holmos-mikroskop/holmos/3D-druck/Positionsnummern mit Liste.PNG

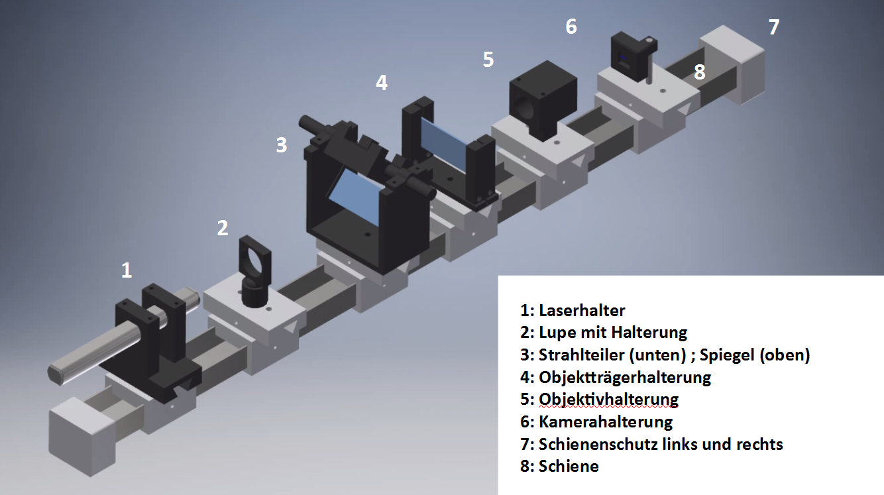
3D-druck/Positionsnummern mit Liste.PNG
