holmos-mikroskop/holmos/doku-img/auswertung-01.png

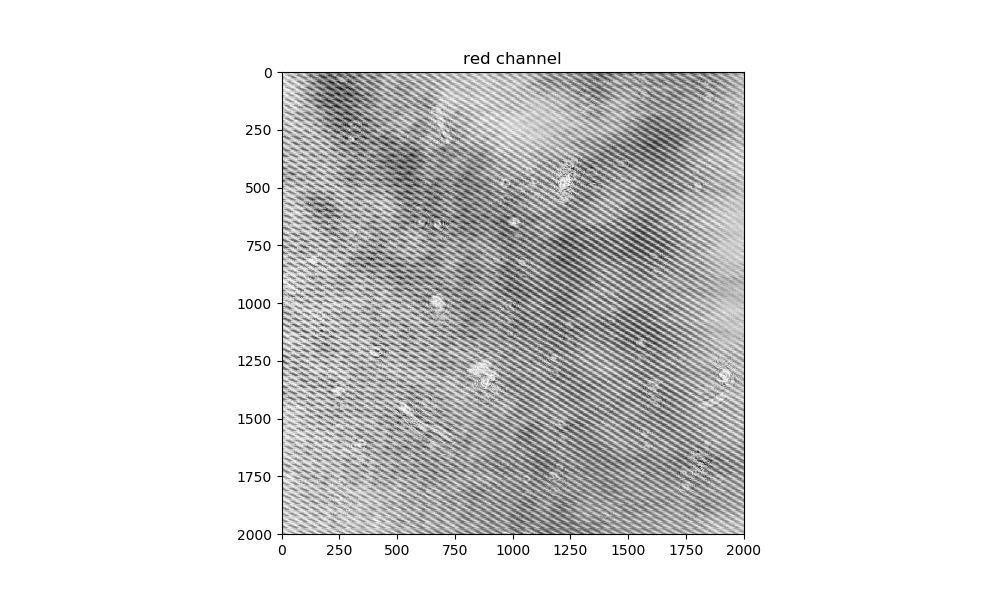
doku-img/auswertung-01.png
