holmos-mikroskop/holmos/doku-img/auswertung-02.png

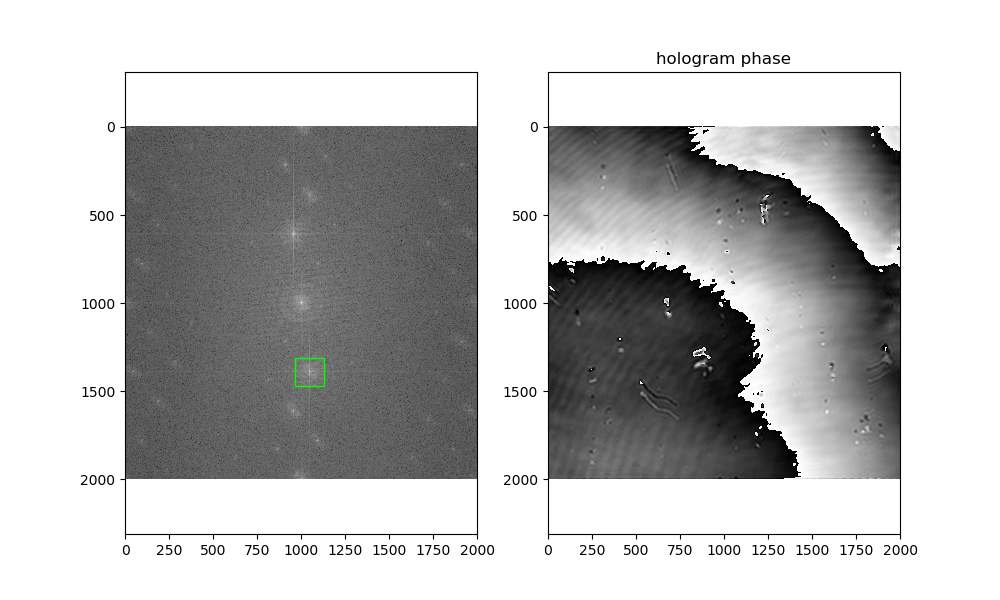
doku-img/auswertung-02.png
