holmos-mikroskop/holmos/doku-img/auswertung-c_001.png

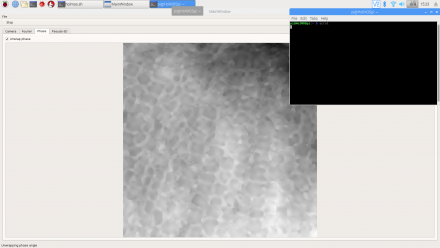
doku-img/auswertung-c_001.png
