holmos-mikroskop/holmos/doku-img/auswertung-c_002.png

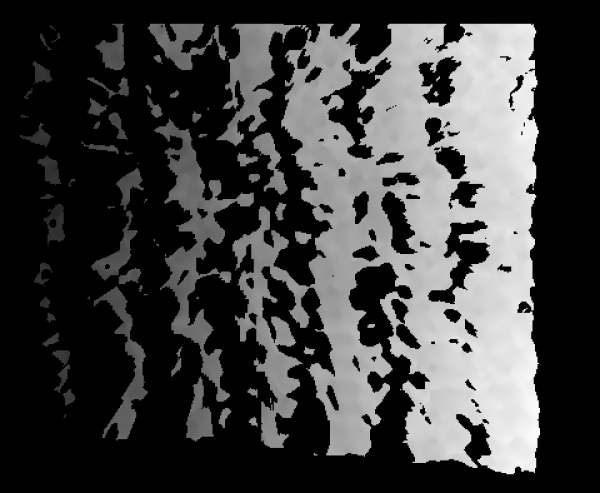
doku-img/auswertung-c_002.png
