holmos-mikroskop/holmos/doku-img/auswertung-c_003.png

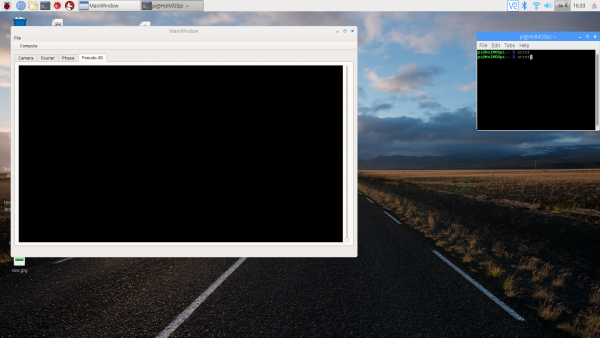
doku-img/auswertung-c_003.png
