holmos-mikroskop/holmos/doku-img/auswertung-c_004.png

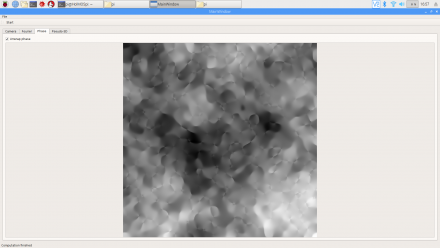
doku-img/auswertung-c_004.png
