holmos-mikroskop/holmos/doku-img/clone_link.jpg

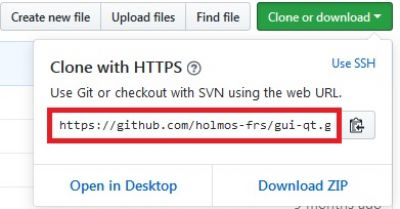
doku-img/clone_link.jpg
