holmos-mikroskop/holmos/doku-img/einfache-auswertung_001.png

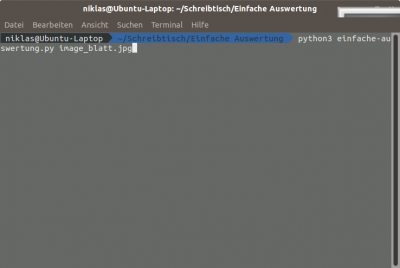
doku-img/einfache-auswertung_001.png
