holmos-mikroskop/holmos/doku-img/einfache-auswertung_002.png

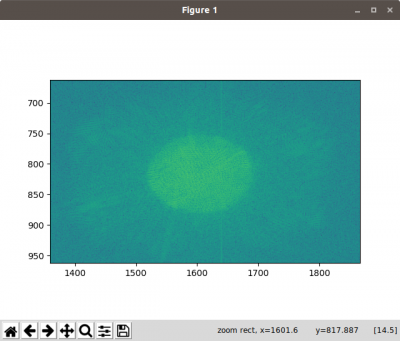
doku-img/einfache-auswertung_002.png
