holmos-mikroskop/holmos/doku-img/einfache-auswertung_003.png

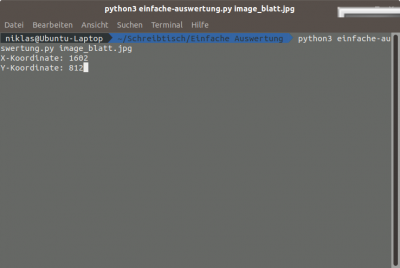
doku-img/einfache-auswertung_003.png
