holmos-mikroskop/holmos/doku-img/einfache-auswertung_005.png

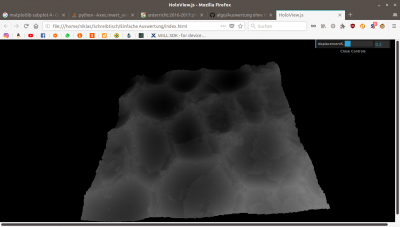
doku-img/einfache-auswertung_005.png
