holmos-mikroskop/holmos/doku-img/erste_interferenz.png

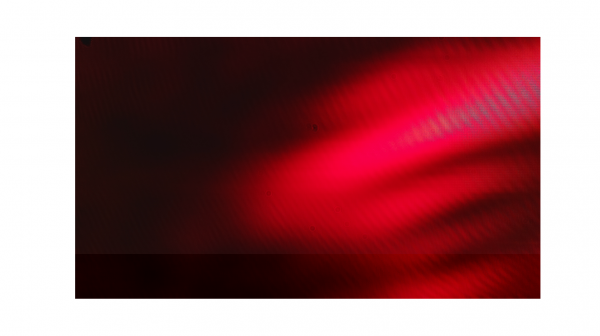
doku-img/erste_interferenz.png
