holmos-mikroskop/holmos/doku-img/first-light.jpg

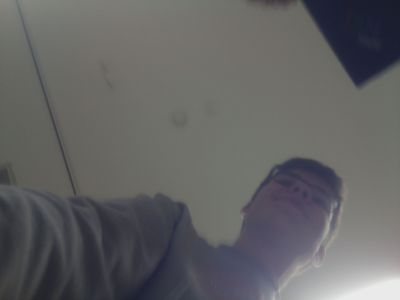
doku-img/first-light.jpg
