holmos-mikroskop/holmos/doku-img/holoview_bsp2_figure1.jpg

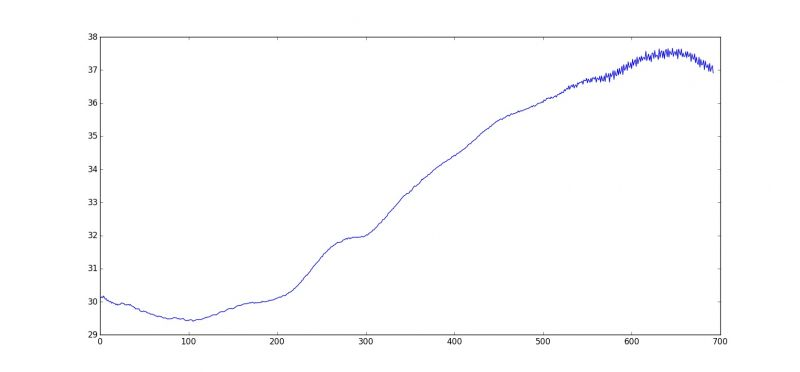
doku-img/holoview_bsp2_figure1.jpg
