holmos-mikroskop/holmos/doku-img/holoview_capture.jpg

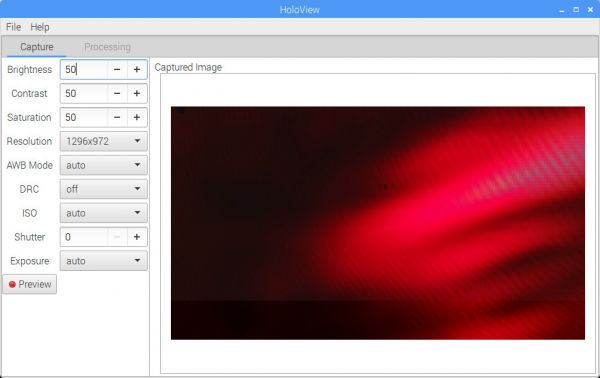
doku-img/holoview_capture.jpg
