holmos-mikroskop/holmos/doku-img/interferometer-001.png

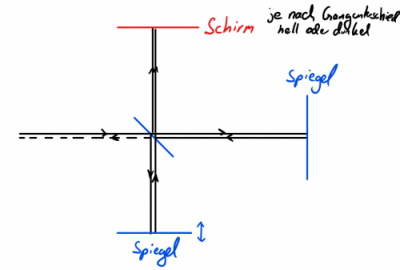
doku-img/interferometer-001.png
