holmos-mikroskop/holmos/doku-img/interferometer-002.jpg

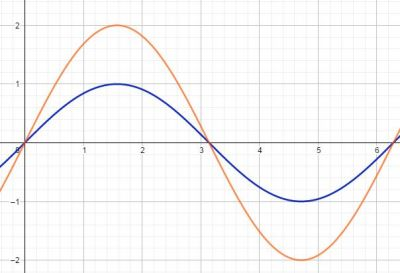
doku-img/interferometer-002.jpg
