holmos-mikroskop/holmos/doku-img/interferometer-003.jpg

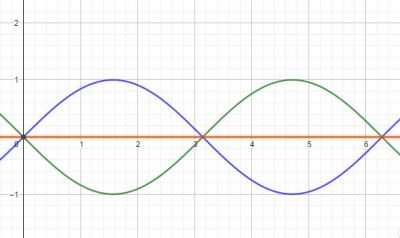
doku-img/interferometer-003.jpg
