holmos-mikroskop/holmos/doku-img/interferometer-004.jpg

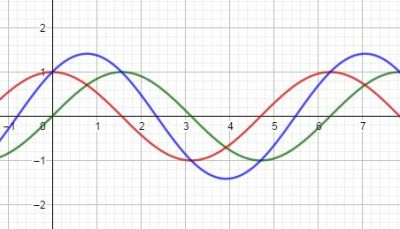
doku-img/interferometer-004.jpg
