holmos-mikroskop/holmos/doku-img/interferometer-006.gif

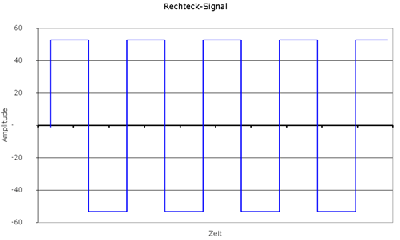
doku-img/interferometer-006.gif
