holmos-mikroskop/holmos/doku-img/interferometer-007.gif

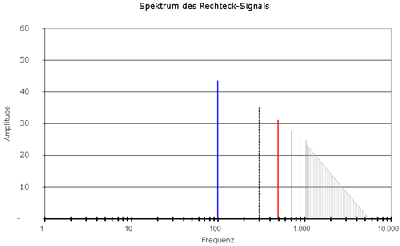
doku-img/interferometer-007.gif
