holmos-mikroskop/holmos/doku-img/interferometer-008.jpg

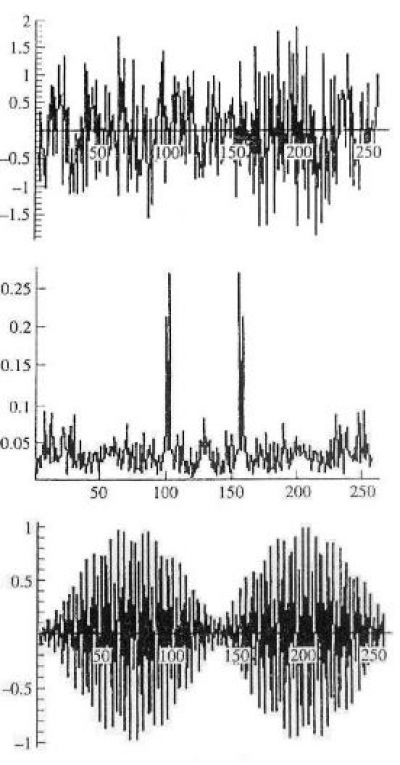
doku-img/interferometer-008.jpg
