holmos-mikroskop/holmos/doku-img/interferometer-009.jpg

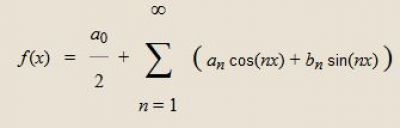
doku-img/interferometer-009.jpg
