holmos-mikroskop/holmos/doku-img/interferometer-010.jpg

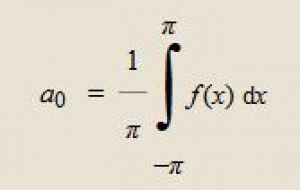
doku-img/interferometer-010.jpg
