holmos-mikroskop/holmos/doku-img/interferometer-011.jpg

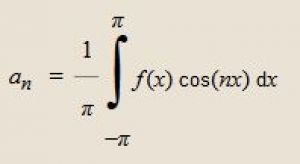
doku-img/interferometer-011.jpg
