holmos-mikroskop/holmos/doku-img/justage-laserdiode/justage-laserdiode-01.jpg

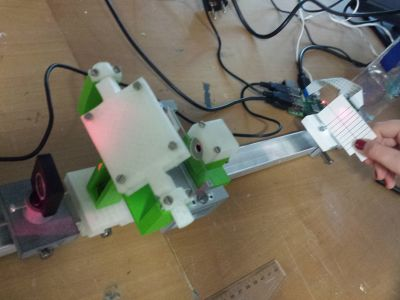
doku-img/justage-laserdiode/justage-laserdiode-01.jpg
