holmos-mikroskop/holmos/doku-img/justage-laserdiode/justage-laserdiode-02.jpg

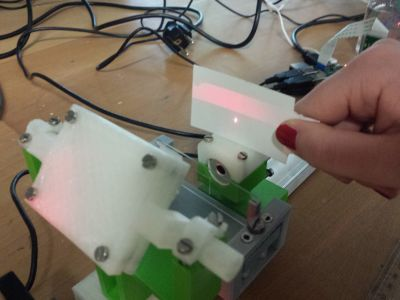
doku-img/justage-laserdiode/justage-laserdiode-02.jpg
