holmos-mikroskop/holmos/doku-img/justage-laserdiode/justage-laserdiode-03.jpg

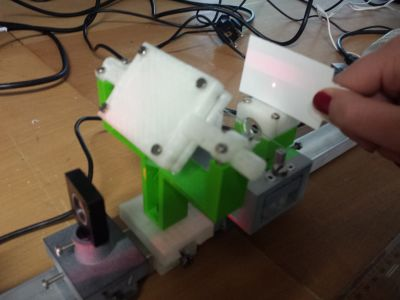
doku-img/justage-laserdiode/justage-laserdiode-03.jpg
