holmos-mikroskop/holmos/doku-img/justage-laserdiode/justage-laserdiode-04.jpg

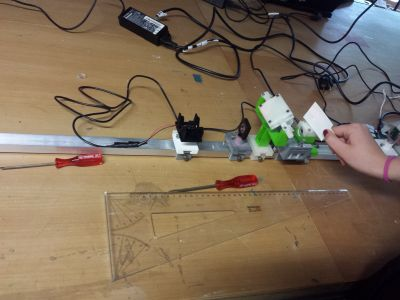
doku-img/justage-laserdiode/justage-laserdiode-04.jpg
