holmos-mikroskop/holmos/doku-img/justage-laserdiode/justage-laserdiode-05.jpg

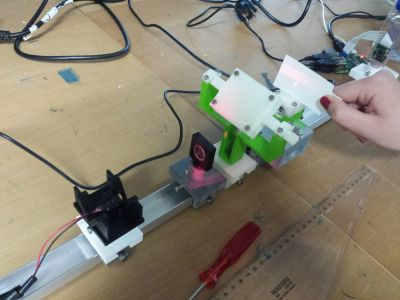
doku-img/justage-laserdiode/justage-laserdiode-05.jpg
