holmos-mikroskop/holmos/doku-img/justage-laserdiode/justage-laserdiode-07.jpg

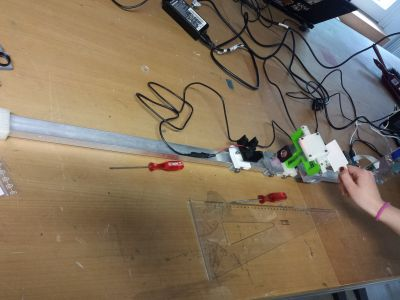
doku-img/justage-laserdiode/justage-laserdiode-07.jpg
