holmos-mikroskop/holmos/doku-img/justage-laserdiode/justage-laserdiode-08.jpg

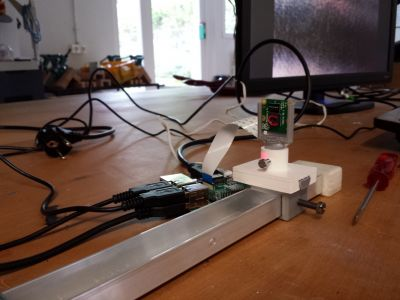
doku-img/justage-laserdiode/justage-laserdiode-08.jpg
