holmos-mikroskop/holmos/doku-img/justage-laserdiode/justage-laserdiode-09.jpg

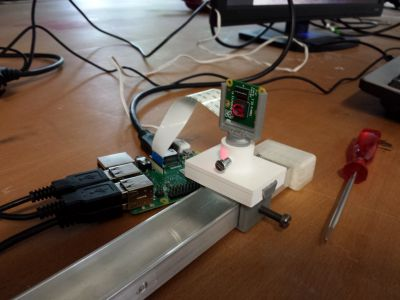
doku-img/justage-laserdiode/justage-laserdiode-09.jpg
