holmos-mikroskop/holmos/doku-img/justage-laserpointer/justage-01.jpg

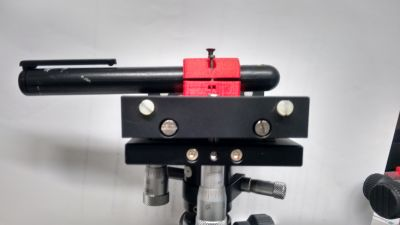
doku-img/justage-laserpointer/justage-01.jpg
