holmos-mikroskop/holmos/doku-img/justage-laserpointer/justage-02.jpg

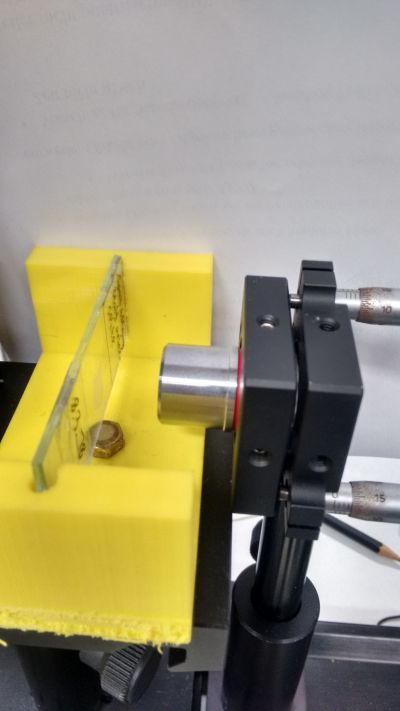
doku-img/justage-laserpointer/justage-02.jpg
