holmos-mikroskop/holmos/doku-img/justage-laserpointer/justage-03.jpg

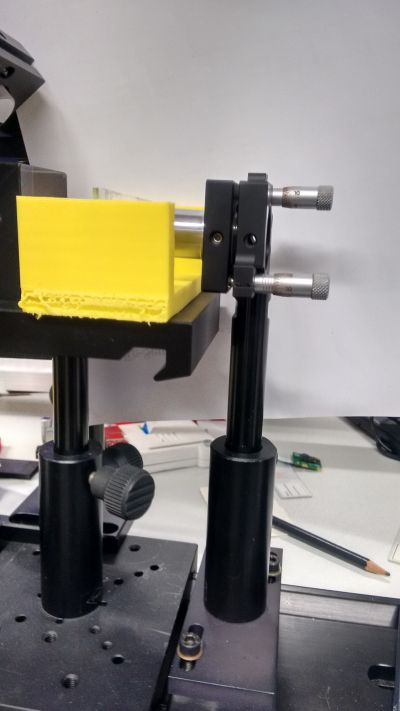
doku-img/justage-laserpointer/justage-03.jpg
