holmos-mikroskop/holmos/doku-img/justage-laserpointer/justage-04.jpg

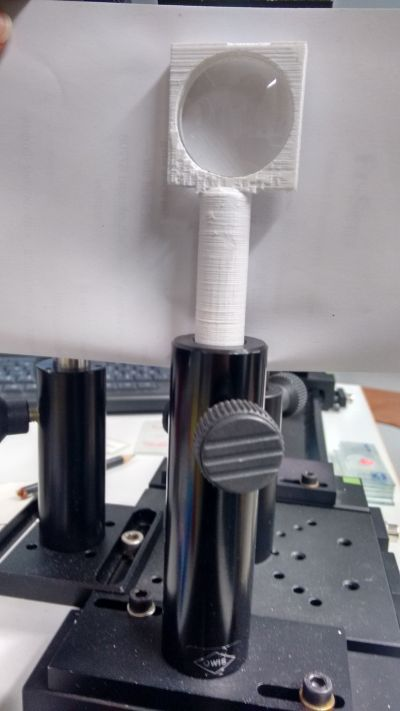
doku-img/justage-laserpointer/justage-04.jpg
