holmos-mikroskop/holmos/doku-img/justage-laserpointer/justage-06.jpg

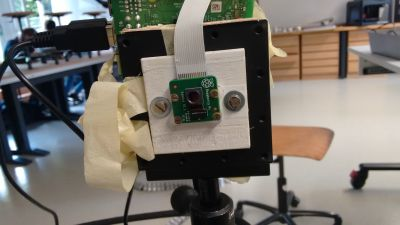
doku-img/justage-laserpointer/justage-06.jpg
