holmos-mikroskop/holmos/doku-img/kamera-anschliessen-01.jpg

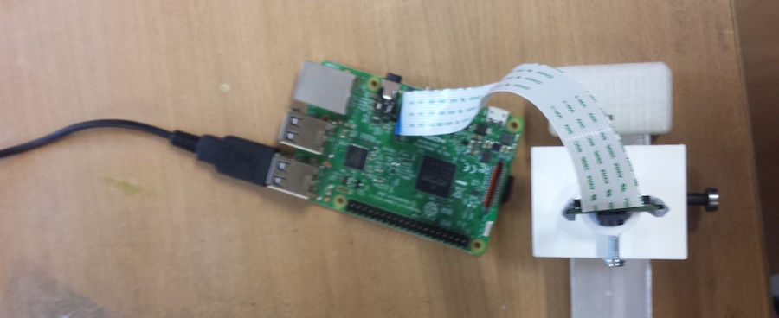
doku-img/kamera-anschliessen-01.jpg
