holmos-mikroskop/holmos/doku-img/kamera-anschliessen-02.jpg

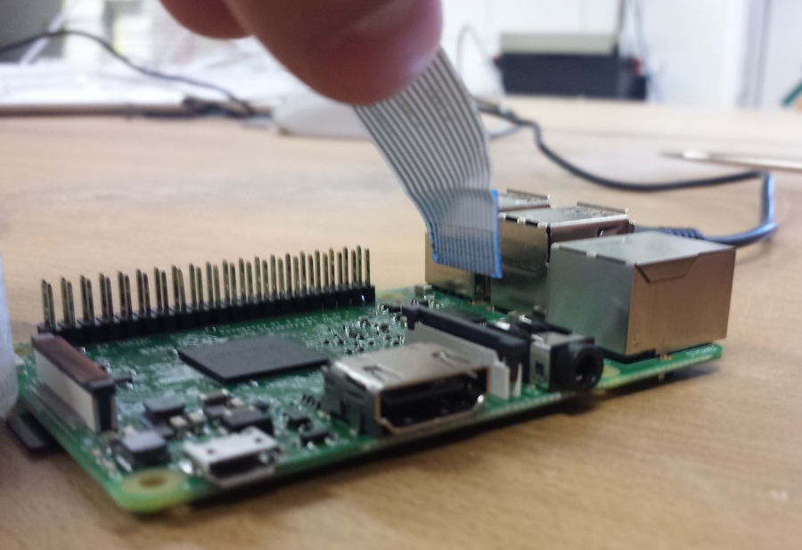
doku-img/kamera-anschliessen-02.jpg
