holmos-mikroskop/holmos/doku-img/praeparate/blattunterseite/digpraeprhoeodiskspalt.jpg

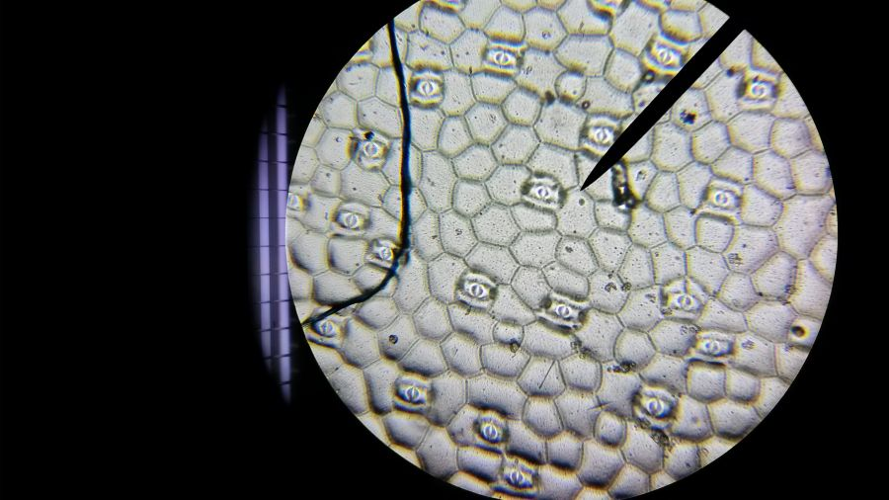
doku-img/praeparate/blattunterseite/digpraeprhoeodiskspalt.jpg
