holmos-mikroskop/holmos/doku-img/praeparate/blattunterseite/negativrhoeodigiprozess-1.png

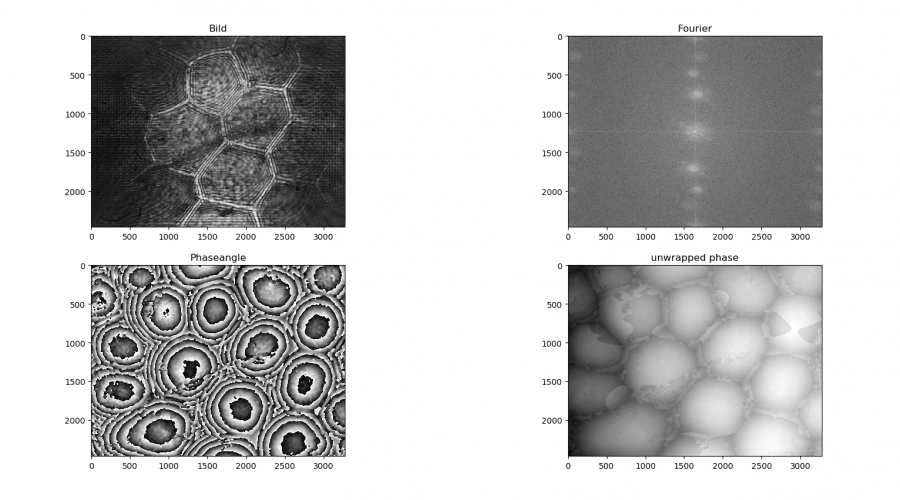
doku-img/praeparate/blattunterseite/negativrhoeodigiprozess-1.png
