holmos-mikroskop/holmos/doku-img/praeparate/blattunterseite/negativrhoeodigiverstetigt3d.png

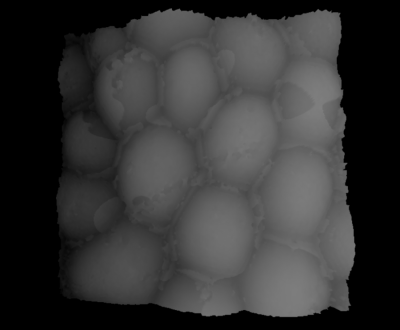
doku-img/praeparate/blattunterseite/negativrhoeodigiverstetigt3d.png
