holmos-mikroskop/holmos/doku-img/praeparate/blattunterseite/negativrhoeodigiverstetigt.png

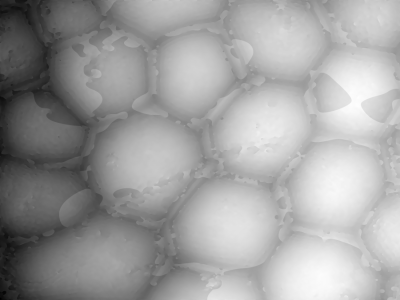
doku-img/praeparate/blattunterseite/negativrhoeodigiverstetigt.png
