holmos-mikroskop/holmos/doku-img/praeparate/chilli/0-chilibluete.jpg

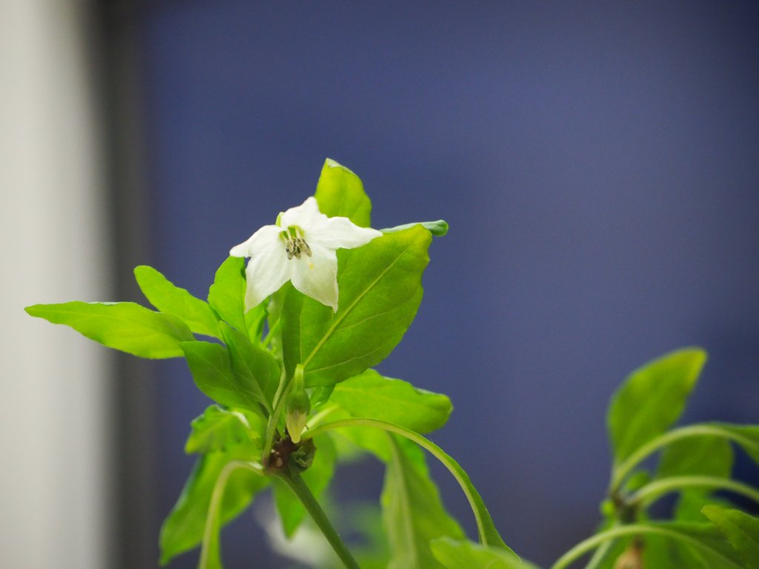
doku-img/praeparate/chilli/0-chilibluete.jpg
