holmos-mikroskop/holmos/doku-img/praeparate/chilli/2-chillipollen-nicht-verstetigt.png

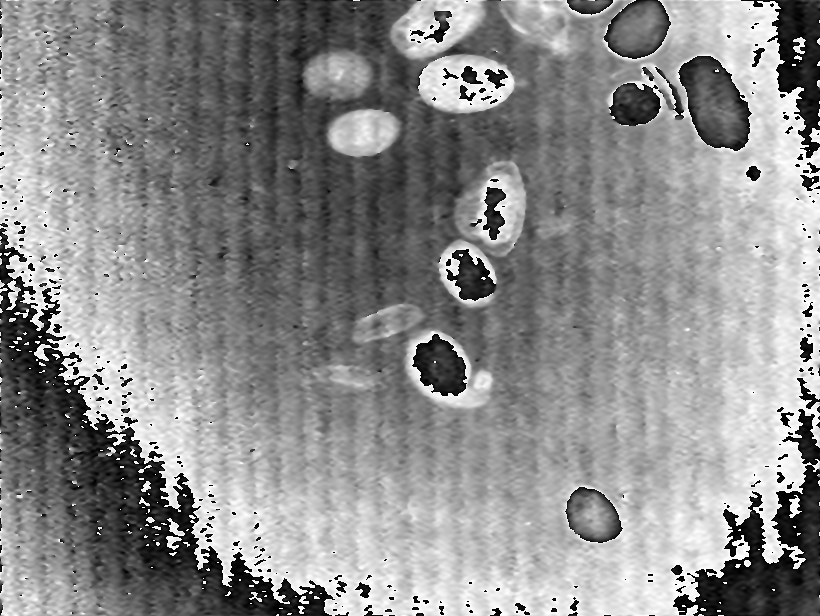
doku-img/praeparate/chilli/2-chillipollen-nicht-verstetigt.png
