holmos-mikroskop/holmos/doku-img/praeparate/chilli/2-chillipollen-verstetigt.png

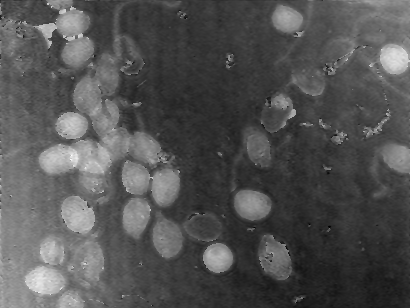
doku-img/praeparate/chilli/2-chillipollen-verstetigt.png
