holmos-mikroskop/holmos/doku-img/praeparate/chilli/6 Surface plot 3D.jpg

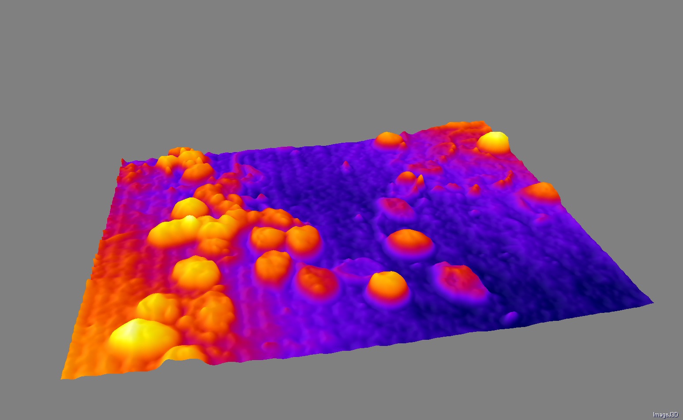
doku-img/praeparate/chilli/6 Surface plot 3D.jpg
