holmos-mikroskop/holmos/doku-img/praeparate/chilli/holmos-2019-01-29-192117-3-fft.png

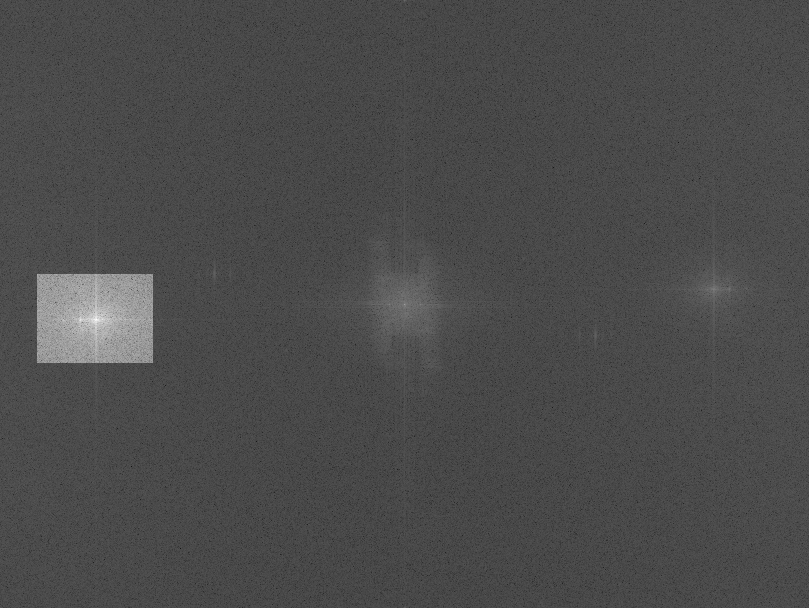
doku-img/praeparate/chilli/holmos-2019-01-29-192117-3-fft.png
