holmos-mikroskop/holmos/doku-img/praeparate/chilli/holmos-2019-01-29-192122-2-objekt+ref.png

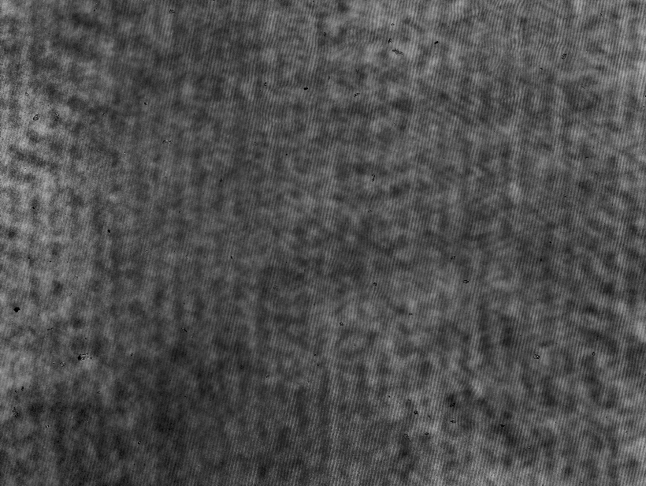
doku-img/praeparate/chilli/holmos-2019-01-29-192122-2-objekt+ref.png
