holmos-mikroskop/holmos/doku-img/praeparate/chilli/holmos-2019-01-29-192136-1-objekt-ohne-ref.png

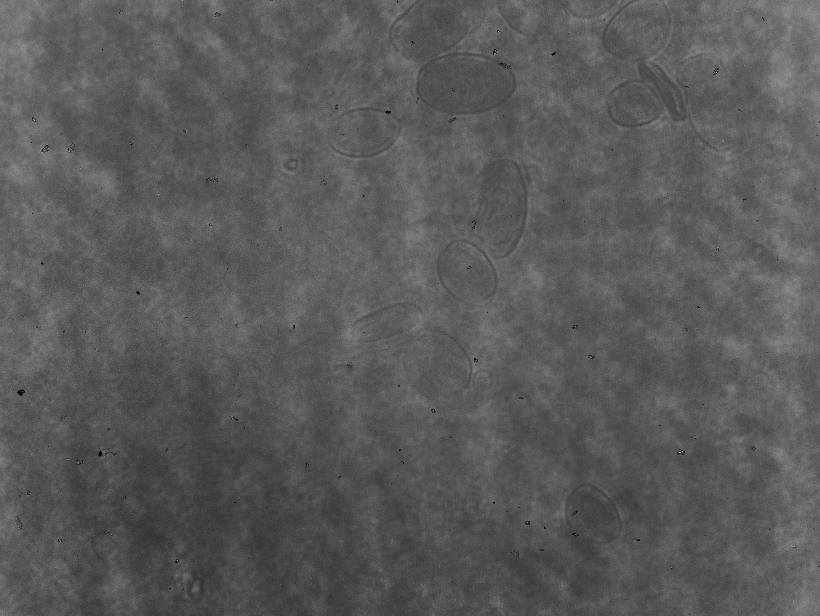
doku-img/praeparate/chilli/holmos-2019-01-29-192136-1-objekt-ohne-ref.png
