holmos-mikroskop/holmos/doku-img/raspberry-pi-draufsicht.jpg

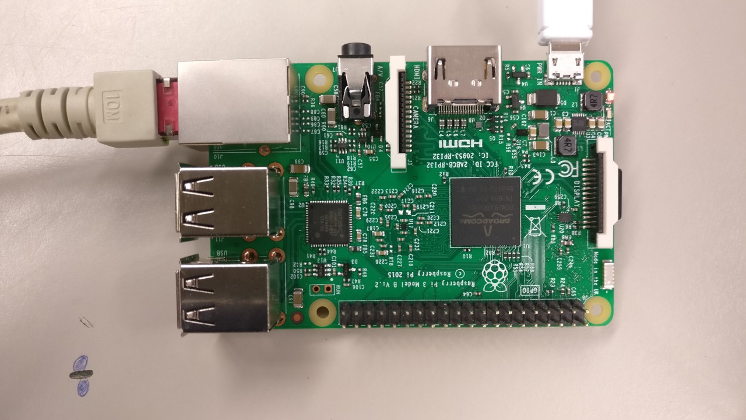
doku-img/raspberry-pi-draufsicht.jpg
