holmos-mikroskop/holmos/doku-img/screenshot-gui-qt-fourier.png

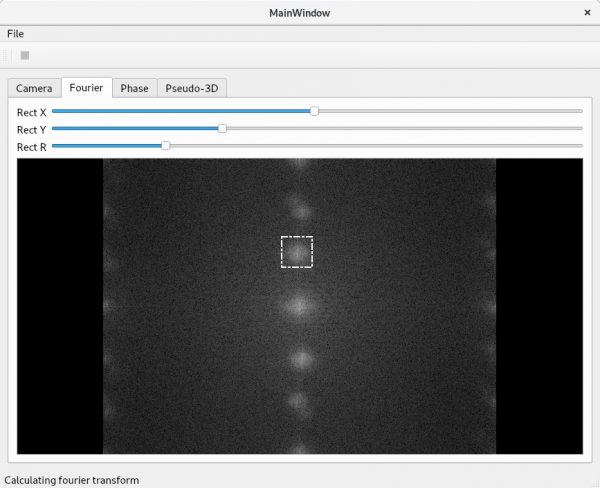
doku-img/screenshot-gui-qt-fourier.png
