holmos-mikroskop/holmos/doku-img/second-image.jpg

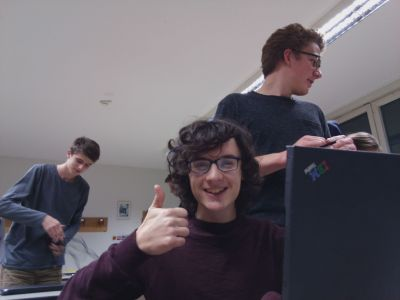
doku-img/second-image.jpg
