holmos-mikroskop/holmos/3D-druck/Schiene_27.5_Neu/3d-Druck_Fertig/Schienenläufer_mit_keil_27.5_15.11.stl

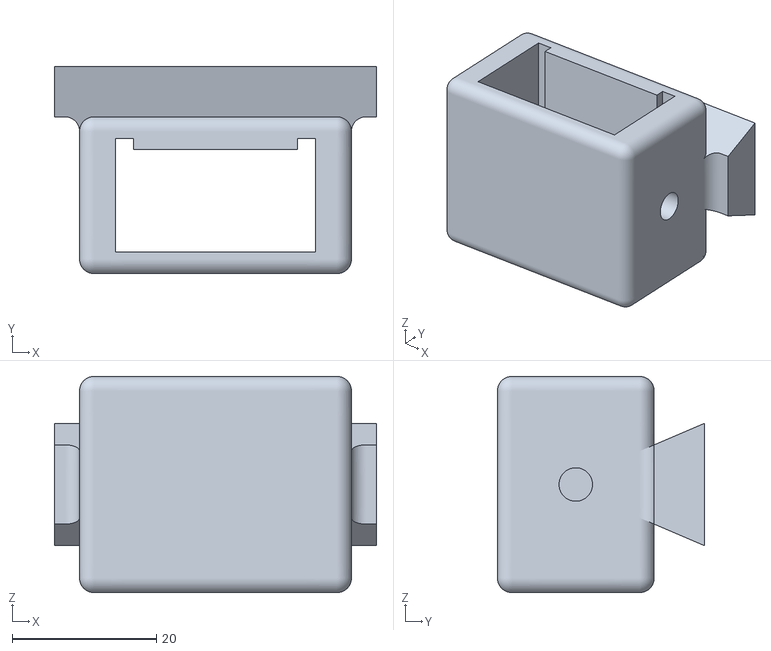
[picture p78: CAD file, 2019-10-29]
3D-druck/Schiene_27.5_Neu/3d-Druck_Fertig/Schienenläufer_mit_keil_27.5_15.11.stl
44.7 x 28.8 x 30.0
