holmos-mikroskop/holmos/3D-druck/Strahlenteiler 26.4/Grundplatte (Neu).stl

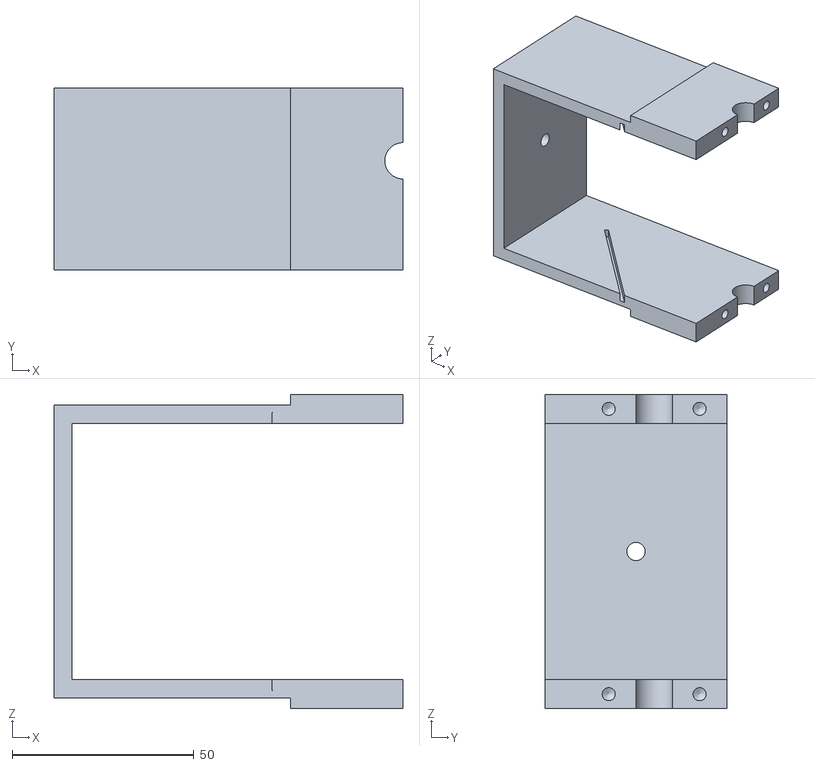
[picture p79: CAD file, 2019-10-29]
3D-druck/Strahlenteiler 26.4/Grundplatte (Neu).stl
96.0 x 50.0 x 86.5
