holmos-mikroskop/holmos/3D-druck/1 Laserhalter/1 Laserhalterung/Mit Schrift/1.1 Laserhalter_Oben.stl

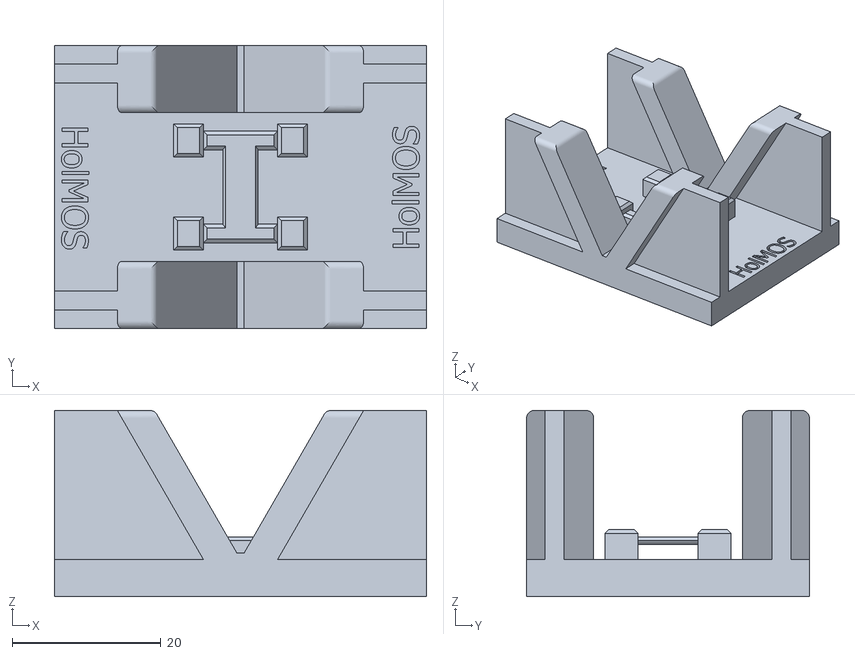
[picture p80: CAD file, 2019-10-29]
3D-druck/1 Laserhalter/1 Laserhalterung/Mit Schrift/1.1 Laserhalter_Oben.stl
50.0 x 38.0 x 25.0
