holmos-mikroskop/holmos/3D-druck/2 Linsenhalterung/2.1 Linsenhalter 16,7 x1.stl

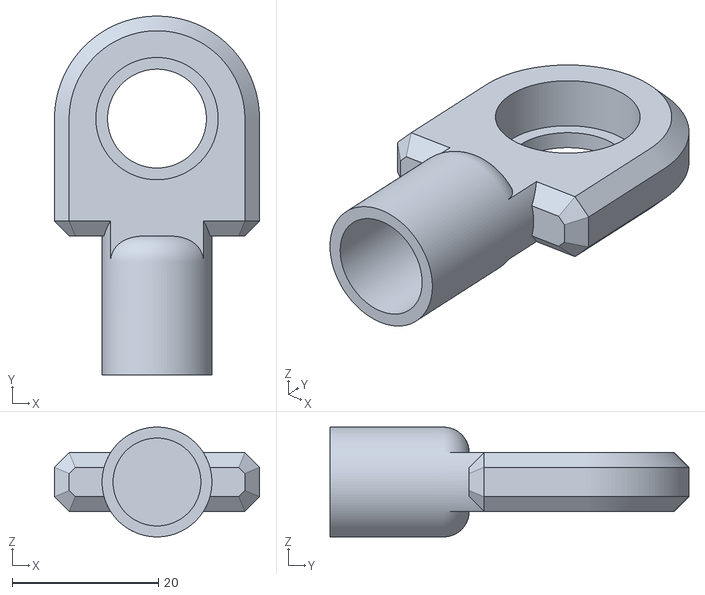
[picture p81: CAD file, 2019-10-29]
3D-druck/2 Linsenhalterung/2.1 Linsenhalter 16,7 x1.stl
28.0 x 49.0 x 15.0
