holmos-mikroskop/holmos/3D-druck/2 Linsenhalterung/Mit Schrift/2.1 Linsenhalter.stl

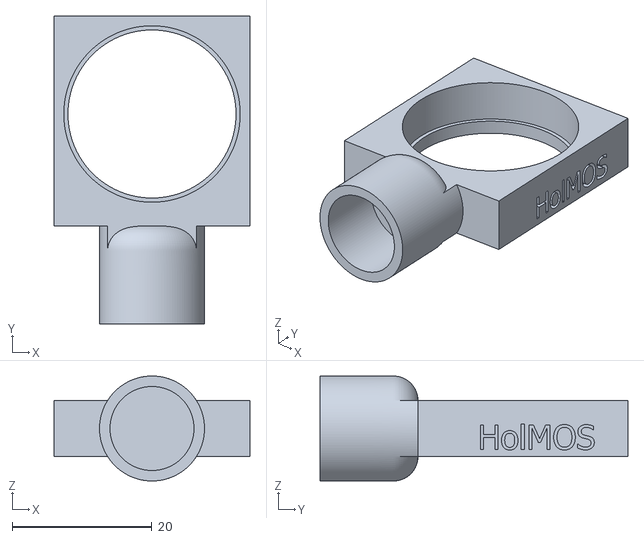
[picture p82: CAD file, 2019-10-29]
3D-druck/2 Linsenhalterung/Mit Schrift/2.1 Linsenhalter.stl
28.0 x 44.0 x 15.0
