holmos-mikroskop/holmos/3D-druck/3 Strahlenteiler/3.3 Klemme.stl

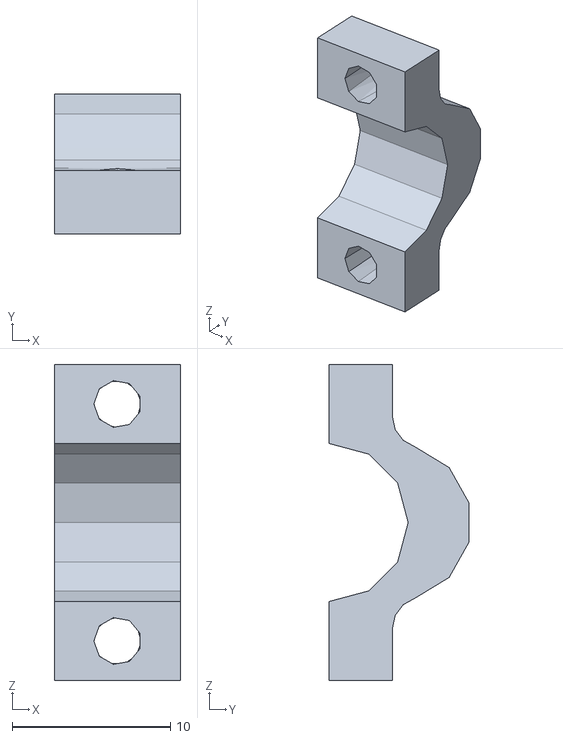
[picture p83: CAD file, 2019-10-29]
3D-druck/3 Strahlenteiler/3.3 Klemme.stl
8.00 x 8.84 x 20.0
