holmos-mikroskop/holmos/3D-druck/4 Objekthalterung/alle alte dateien/Objektträgerhalter 2 6,15mm.stl

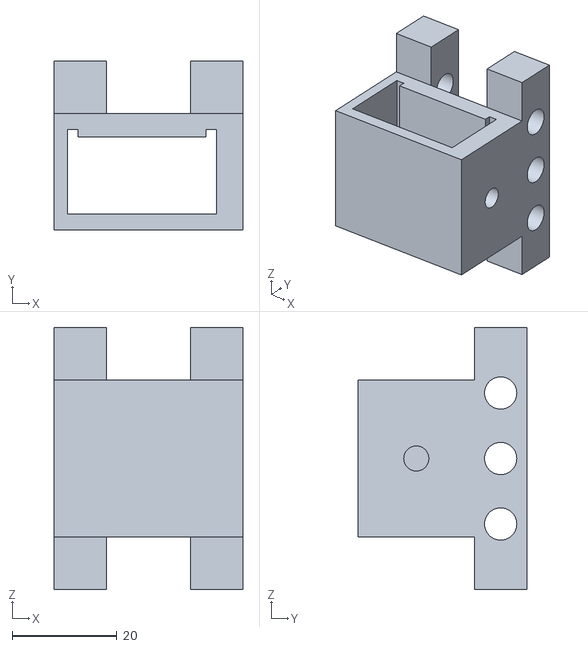
[picture p84: CAD file, 2019-10-29]
3D-druck/4 Objekthalterung/alle alte dateien/Objektträgerhalter 2 6,15mm.stl
36.0 x 32.2 x 50.0
