holmos-mikroskop/holmos/3D-druck/4 Objekthalterung/Finale Dateien/Objektträgerhalter 1.stl

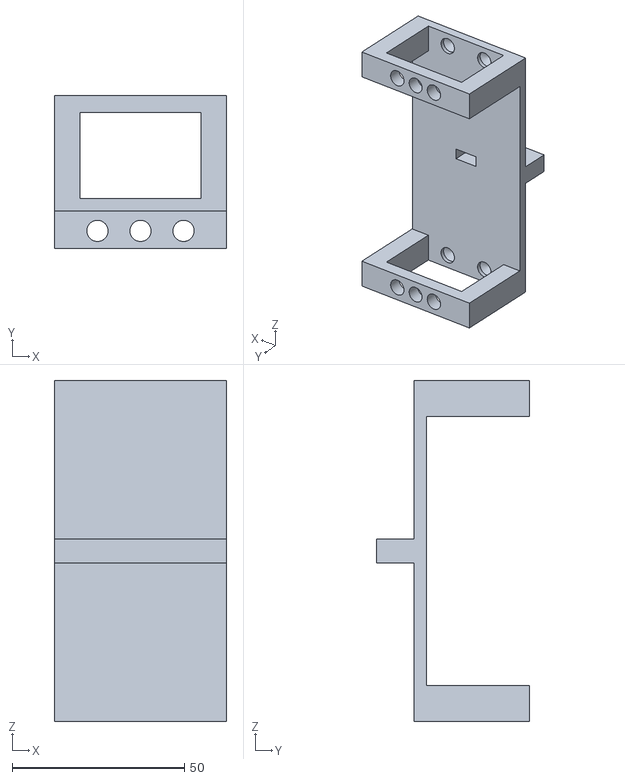
[picture p85: CAD file, 2019-10-29]
3D-druck/4 Objekthalterung/Finale Dateien/Objektträgerhalter 1.stl
50.0 x 44.5 x 99.0
