holmos-mikroskop/holmos/3D-druck/5 Objektivhalterung/5 Objektivhalterung/5.1 Objektivhalterung unten 29112018.stl

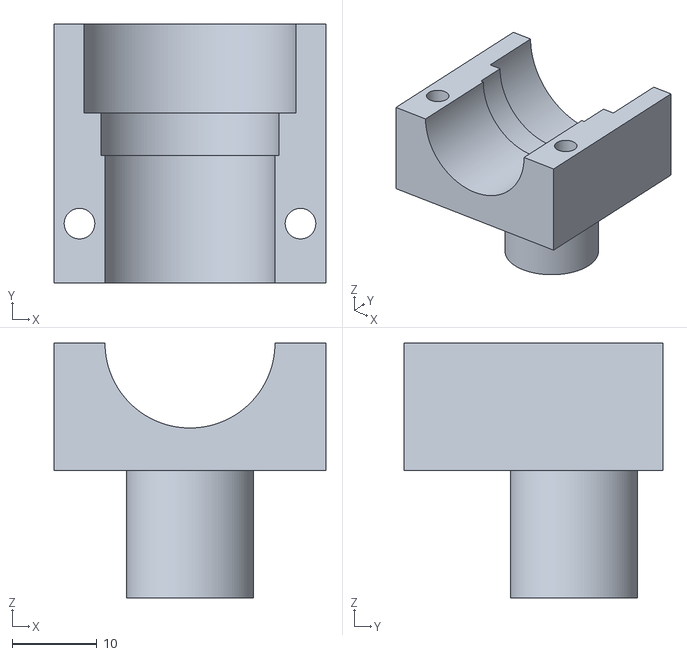
[picture p86: CAD file, 2019-10-29]
3D-druck/5 Objektivhalterung/5 Objektivhalterung/5.1 Objektivhalterung unten 29112018.stl
32.0 x 30.5 x 30.0
