holmos-mikroskop/holmos/3D-druck/5 Objektivhalterung/5 Objektivhalterung/Mit Schrift/5.1 Objektivhalterung_Unten.stl

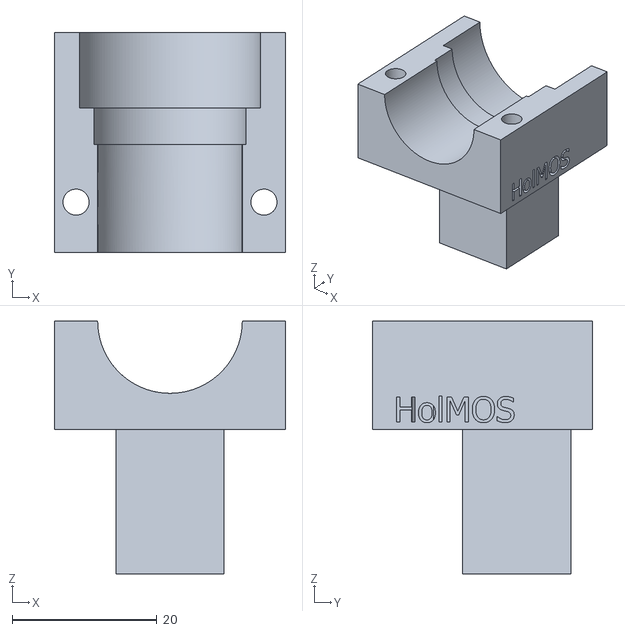
[picture p87: CAD file, 2019-10-29]
3D-druck/5 Objektivhalterung/5 Objektivhalterung/Mit Schrift/5.1 Objektivhalterung_Unten.stl
32.0 x 30.5 x 35.0
