holmos-mikroskop/holmos/3D-druck/5 Objektivhalterung/unterteil.stl

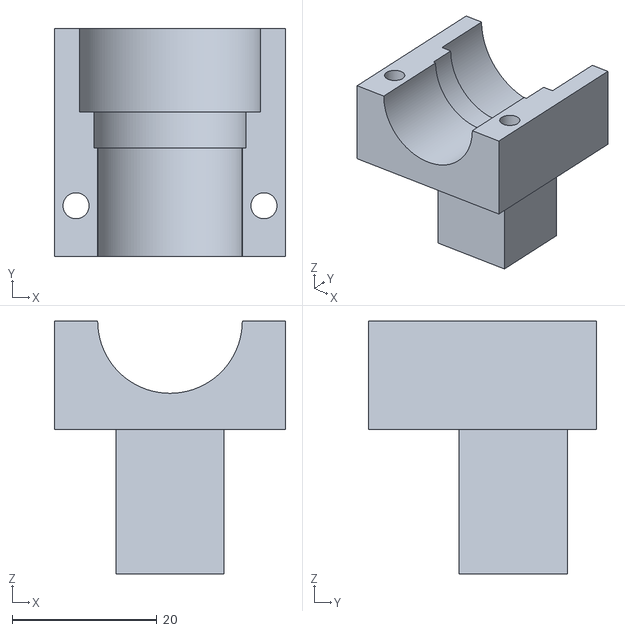
[picture p88: CAD file, 2019-10-29]
3D-druck/5 Objektivhalterung/unterteil.stl
32.0 x 31.5 x 35.0
