holmos-mikroskop/holmos/3D-druck/7 Grundkonstruktion/Mit Schrift/7.2 Schienenläufer.stl

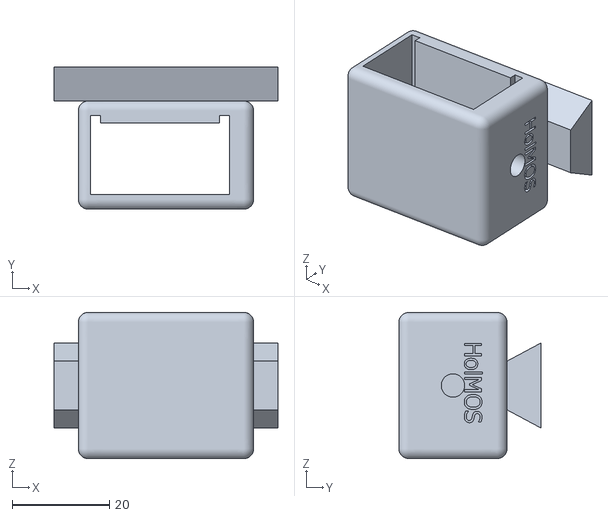
[picture p89: CAD file, 2019-10-29]
3D-druck/7 Grundkonstruktion/Mit Schrift/7.2 Schienenläufer.stl
46.0 x 29.2 x 30.0
