holmos-mikroskop/holmos/3D-druck/Kamerahalter 03.5/Raspberrycamhalter oberteil.stl

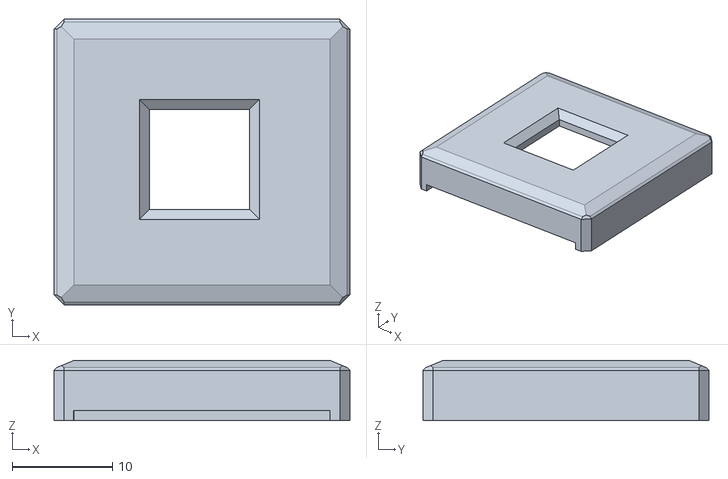
[picture p90: CAD file, 2019-10-29]
3D-druck/Kamerahalter 03.5/Raspberrycamhalter oberteil.stl
29.5 x 28.5 x 6.00
