holmos-mikroskop/holmos/3D-druck/Schiene_27.5_Neu/3d-Druck_Fertig/Schienenläuderaufsatz_15.11..stl

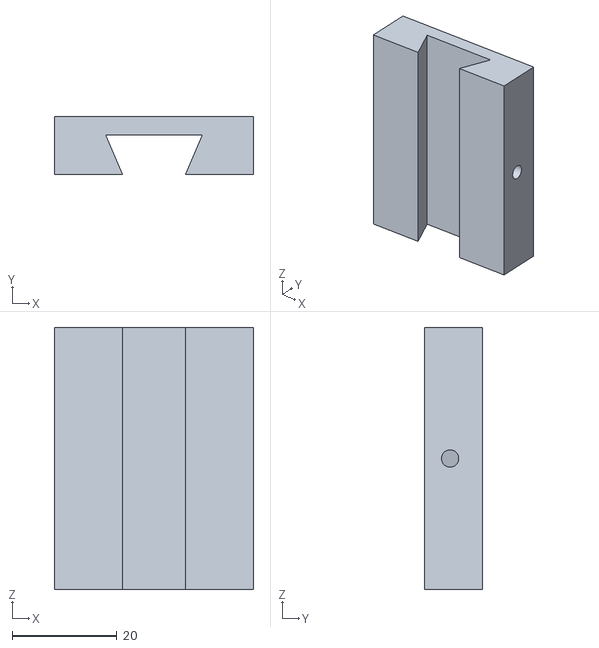
[picture p91: CAD file, 2019-10-29]
3D-druck/Schiene_27.5_Neu/3d-Druck_Fertig/Schienenläuderaufsatz_15.11..stl
38.0 x 11.0 x 50.0
