holmos-mikroskop/holmos/3D-druck/STL-Dateien/3.2 Spiegelhalter_klein x1.stl

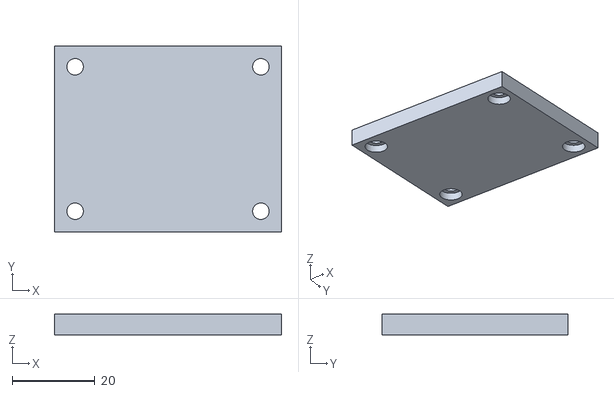
[picture p92: CAD file, 2019-10-29]
3D-druck/STL-Dateien/3.2 Spiegelhalter_klein x1.stl
55.0 x 45.0 x 5.00
