holmos-mikroskop/holmos/3D-druck/1 Laserhalter/1 Laserhalterung/1.2 Laserhalter Mittelteil 29112018.stl

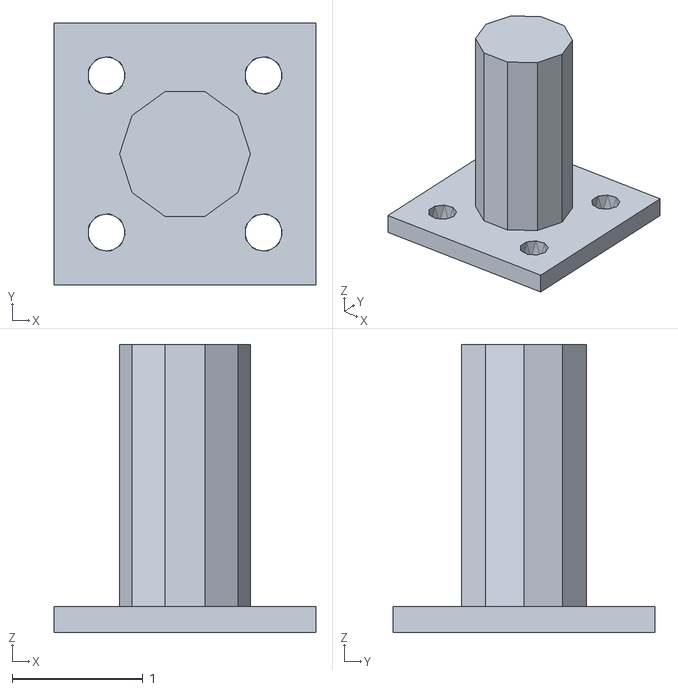
[picture p93: CAD file, 2019-10-29]
3D-druck/1 Laserhalter/1 Laserhalterung/1.2 Laserhalter Mittelteil 29112018.stl
2.00 x 2.00 x 2.20
