holmos-mikroskop/holmos/3D-druck/1 Laserhalter/1 Laserhalterung/Mit Schrift/1.2 Laserhalter_Mitte.stl

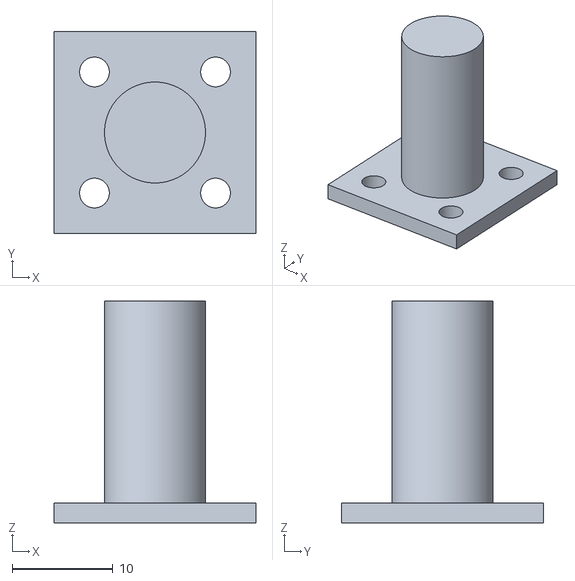
[picture p94: CAD file, 2019-10-29]
3D-druck/1 Laserhalter/1 Laserhalterung/Mit Schrift/1.2 Laserhalter_Mitte.stl
20.0 x 20.0 x 22.0
