holmos-mikroskop/holmos/3D-druck/3 Strahlenteiler/3.1 Neue Grundplatte.stl

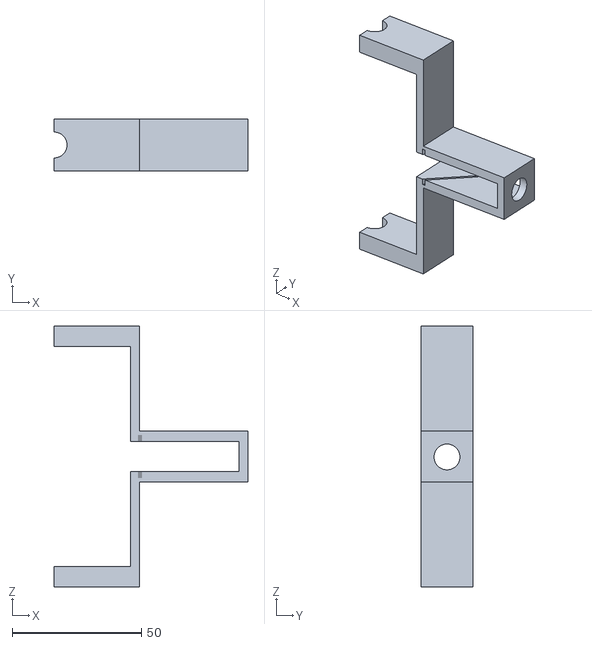
[picture p95: CAD file, 2019-10-29]
3D-druck/3 Strahlenteiler/3.1 Neue Grundplatte.stl
75.0 x 20.0 x 101.0
