holmos-mikroskop/holmos/3D-druck/7 Grundkonstruktion/Mit Schrift/7.1 Schlitten.stl

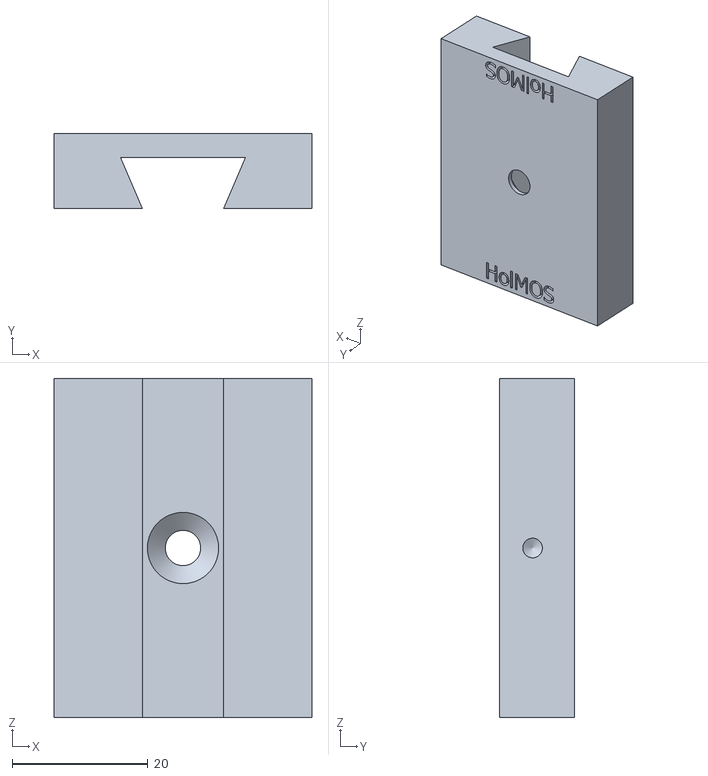
[picture p96: CAD file, 2019-10-29]
3D-druck/7 Grundkonstruktion/Mit Schrift/7.1 Schlitten.stl
38.0 x 11.0 x 50.0
