holmos-mikroskop/holmos/3D-druck/4 Objekthalterung/alle alte dateien/Objekthalter.stl

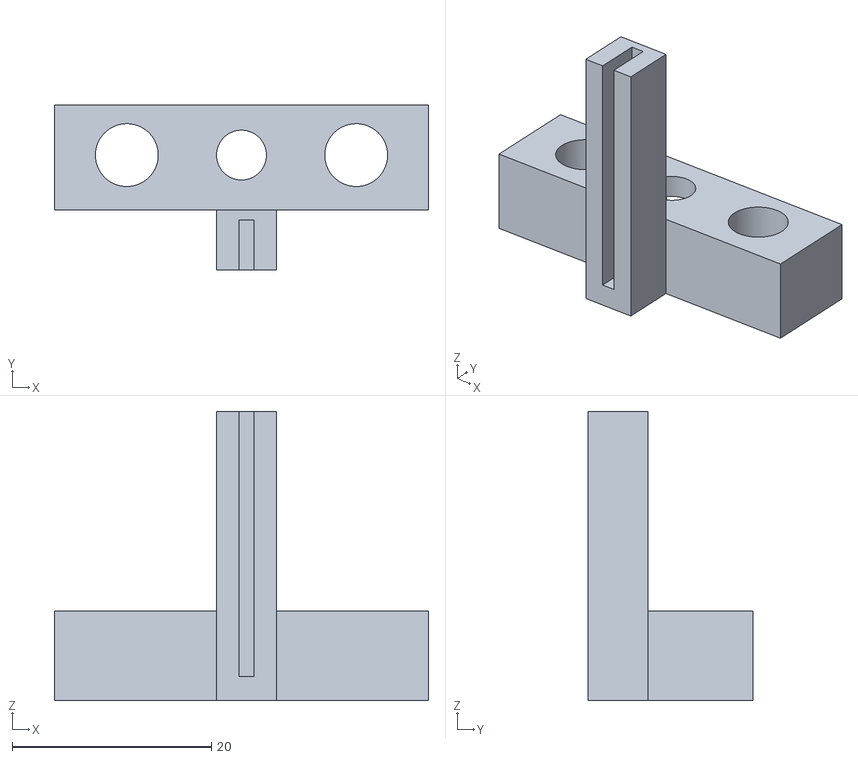
[picture p97: CAD file, 2019-10-29]
3D-druck/4 Objekthalterung/alle alte dateien/Objekthalter.stl
37.5 x 16.5 x 29.0
