holmos-mikroskop/holmos/3D-druck/Objektträgerhalter stl/Objektträgerhalter 2.stl

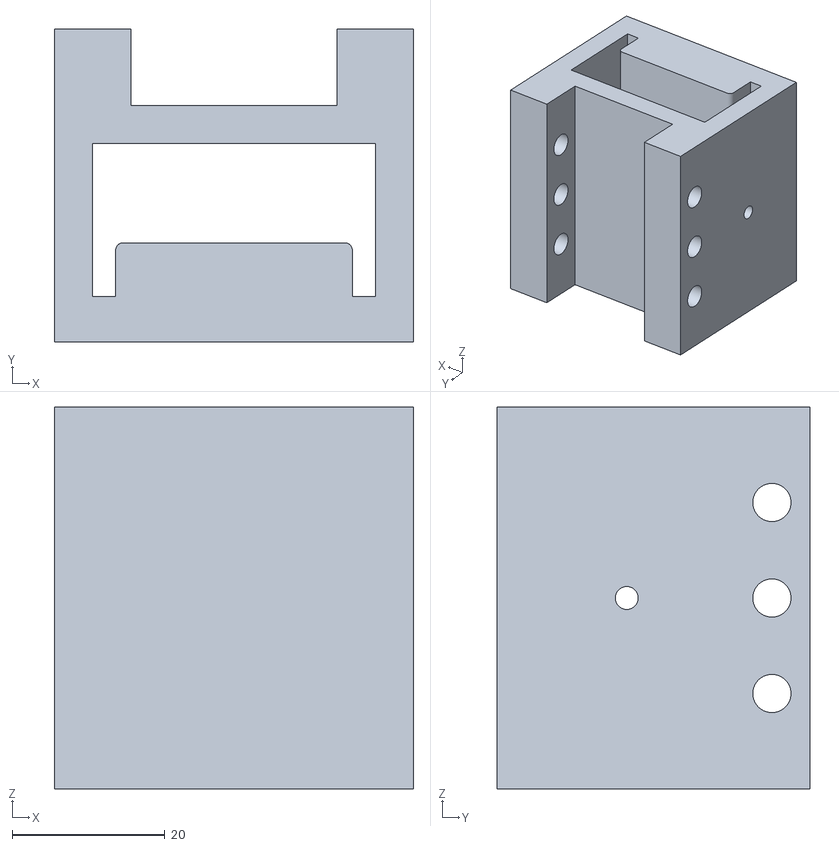
[picture p98: CAD file, 2019-10-29]
3D-druck/Objektträgerhalter stl/Objektträgerhalter 2.stl
47.0 x 41.0 x 50.0
