holmos-mikroskop/holmos/3D-druck/1 Laserhalter/1 Laserhalterung/1.3 Laserhalter Unterteil 29112018.stl

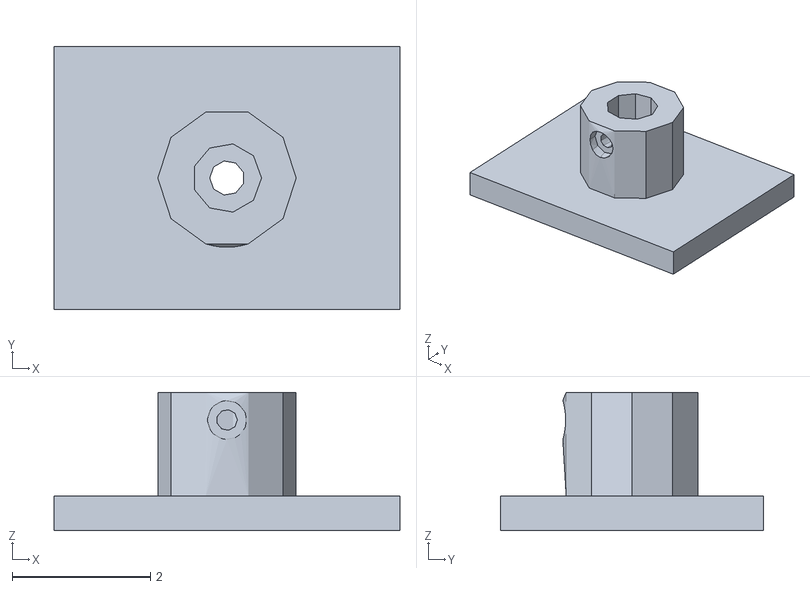
[picture p99: CAD file, 2019-10-29]
3D-druck/1 Laserhalter/1 Laserhalterung/1.3 Laserhalter Unterteil 29112018.stl
5.00 x 3.80 x 2.00
