holmos-mikroskop/holmos/3D-druck/7 Grundkonstruktion/7.2 Schienenläufer-1.stl

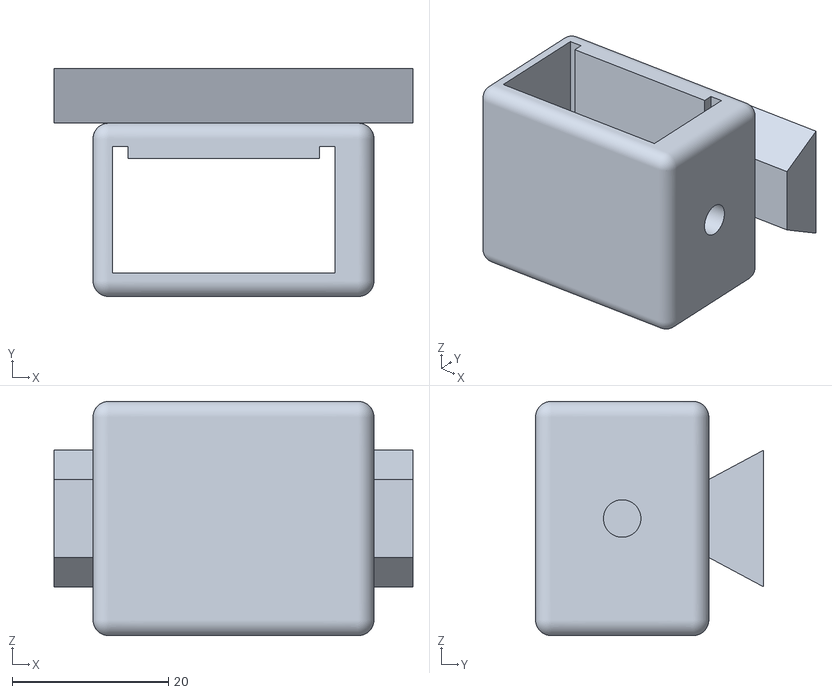
[picture p100: CAD file, 2019-10-29]
3D-druck/7 Grundkonstruktion/7.2 Schienenläufer-1.stl
46.0 x 29.2 x 30.0
