holmos-mikroskop/holmos/3D-druck/7 Grundkonstruktion/7.3 Endhalterung Schiene.stl

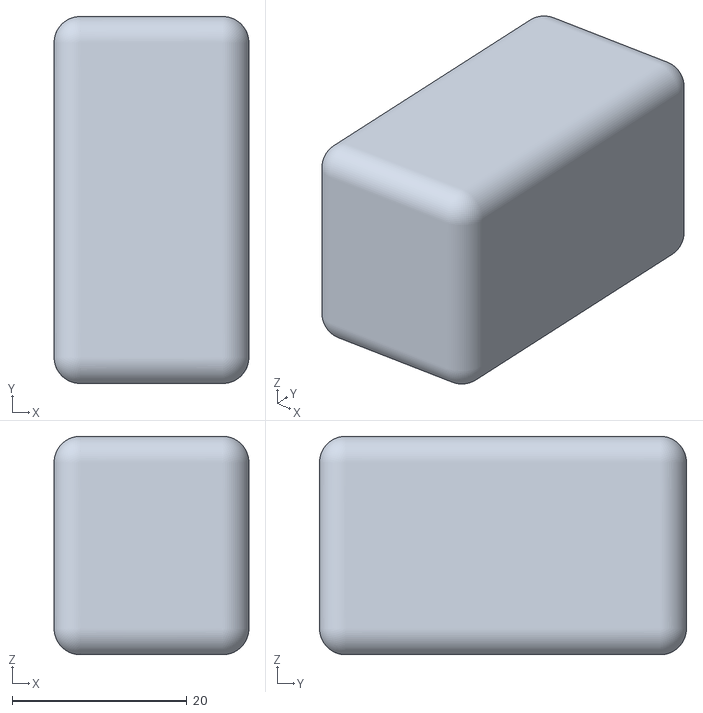
[picture p101: CAD file, 2019-10-29]
3D-druck/7 Grundkonstruktion/7.3 Endhalterung Schiene.stl
22.3 x 42.0 x 25.0
